grimmpp/audiobox-for-kids/case/OpenscadCase1.png

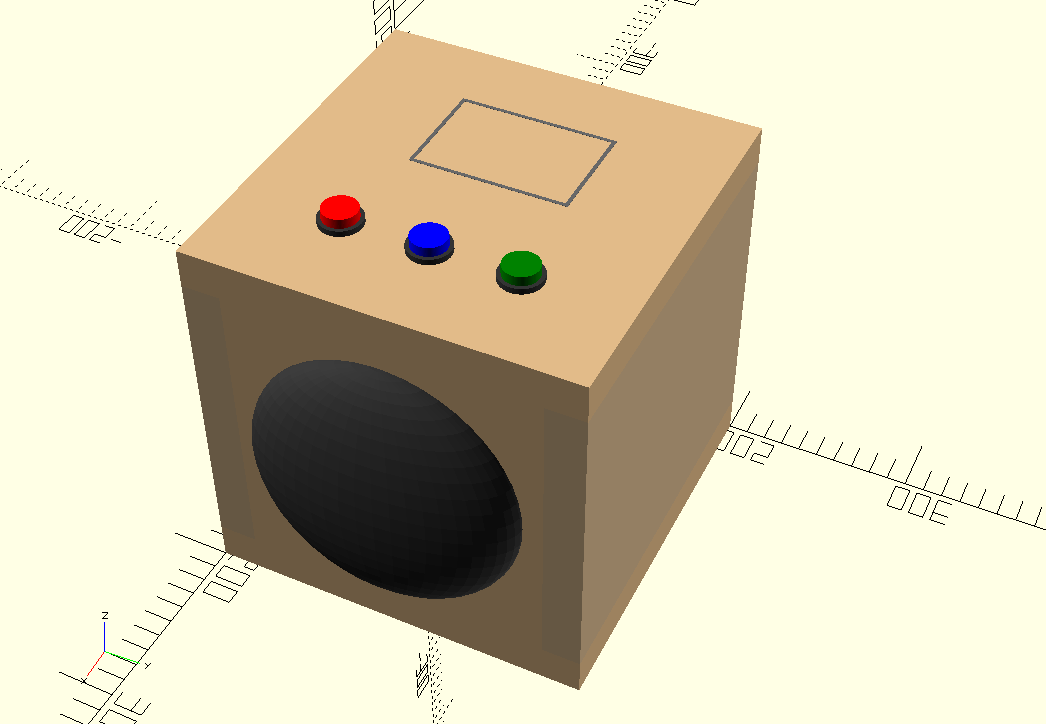
case/OpenscadCase1.png
