grimmpp/audiobox-for-kids/case/OpenscadCase2.png

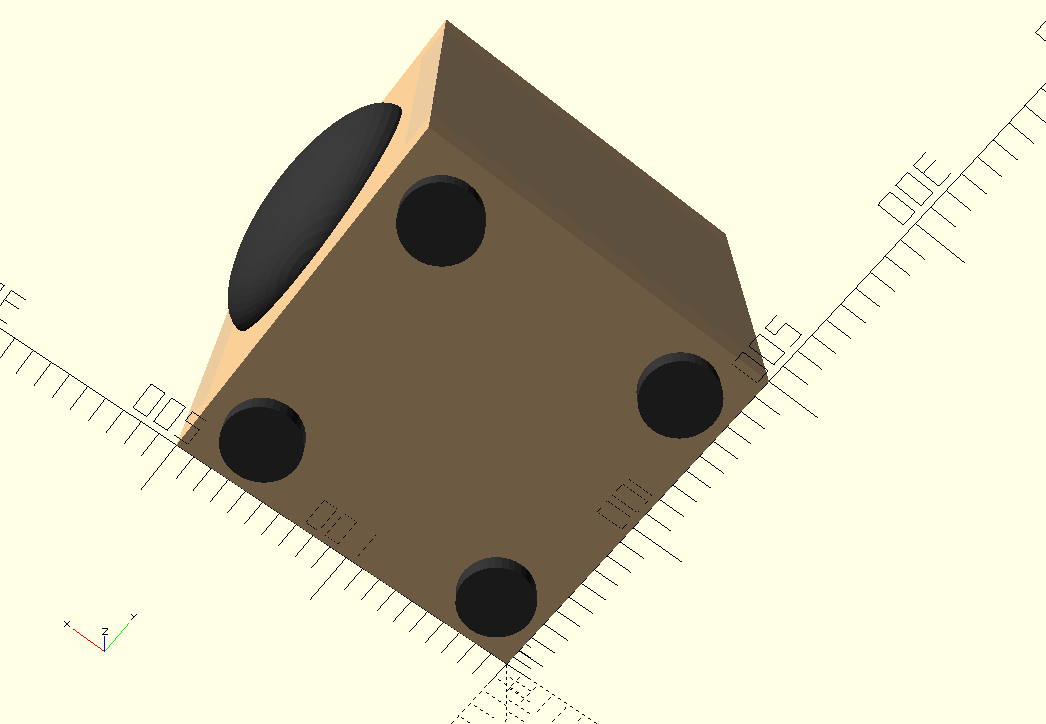
case/OpenscadCase2.png
