grimmpp/audiobox-for-kids/case/OpenscadCase3.png

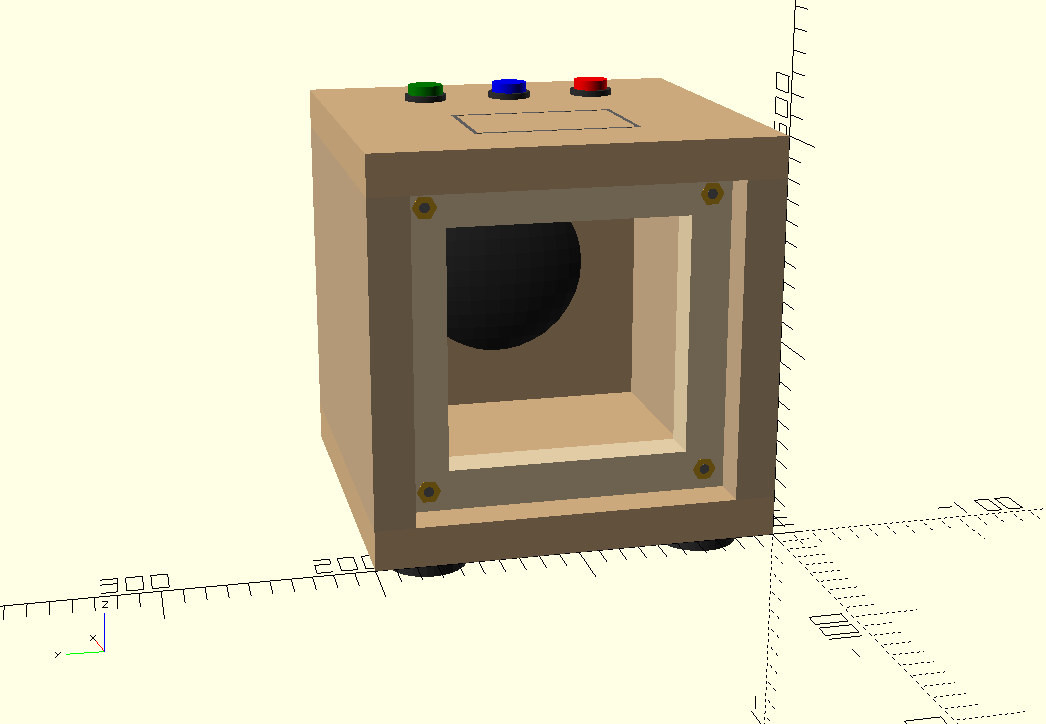
case/OpenscadCase3.png
