grimmpp/audiobox-for-kids/pics/20190909_121117.jpg

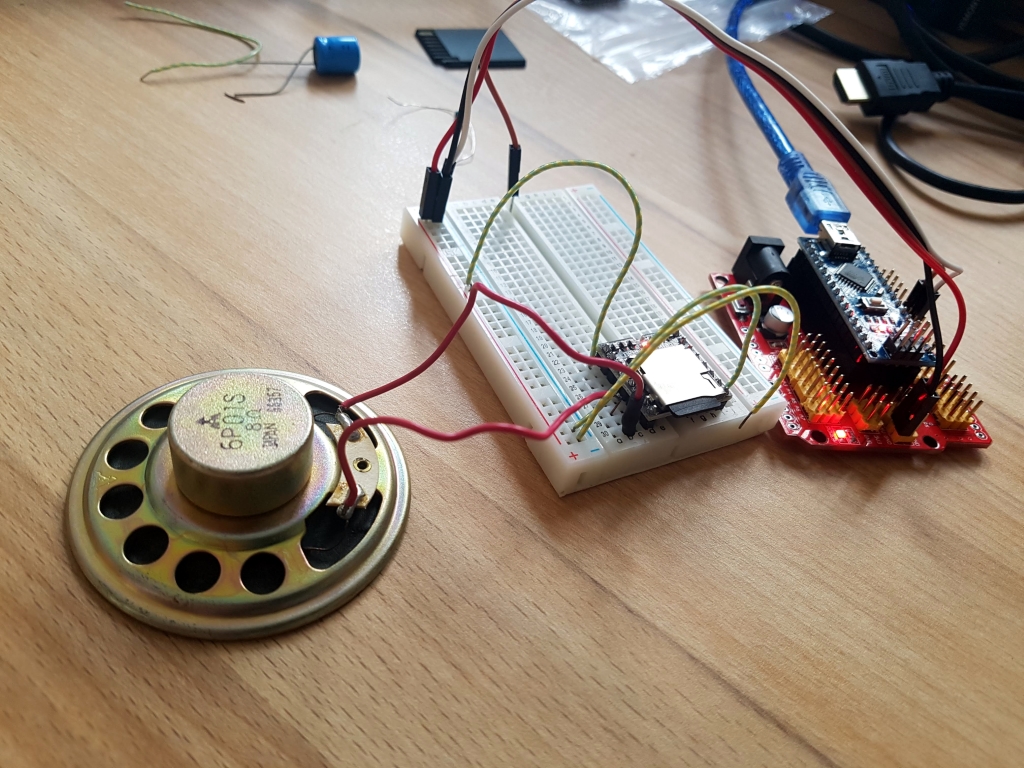
pics/20190909_121117.jpg
