grimmpp/audiobox-for-kids/pics/20190913_085506.jpg

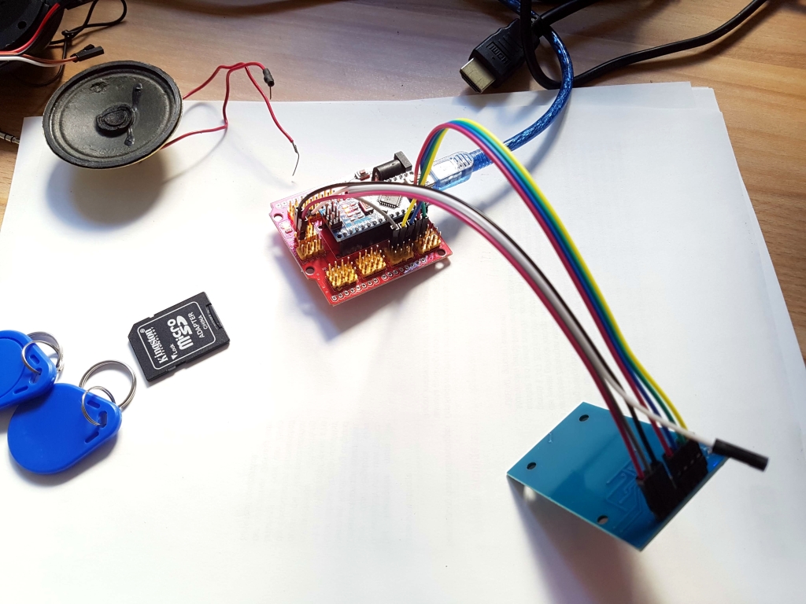
pics/20190913_085506.jpg
