grimmpp/audiobox-for-kids/pics/20190919_153926.jpg

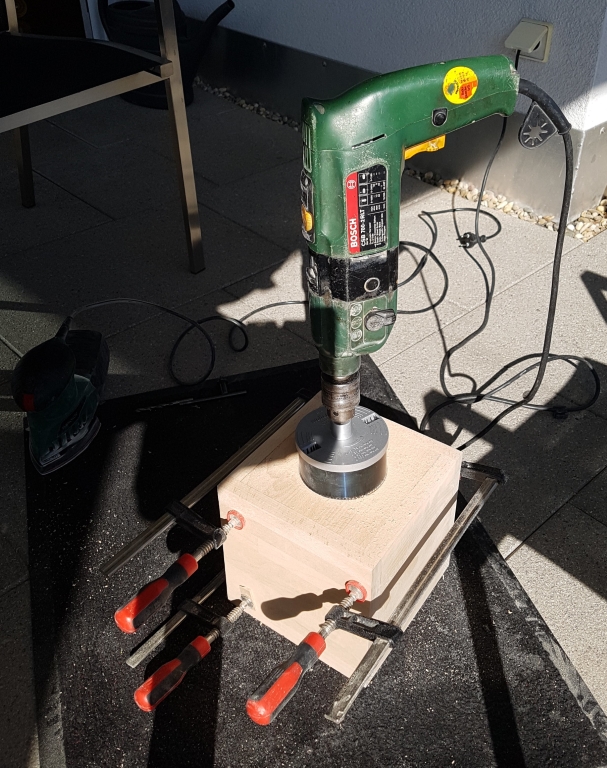
pics/20190919_153926.jpg
