grimmpp/audiobox-for-kids/pics/20190919_154714.jpg

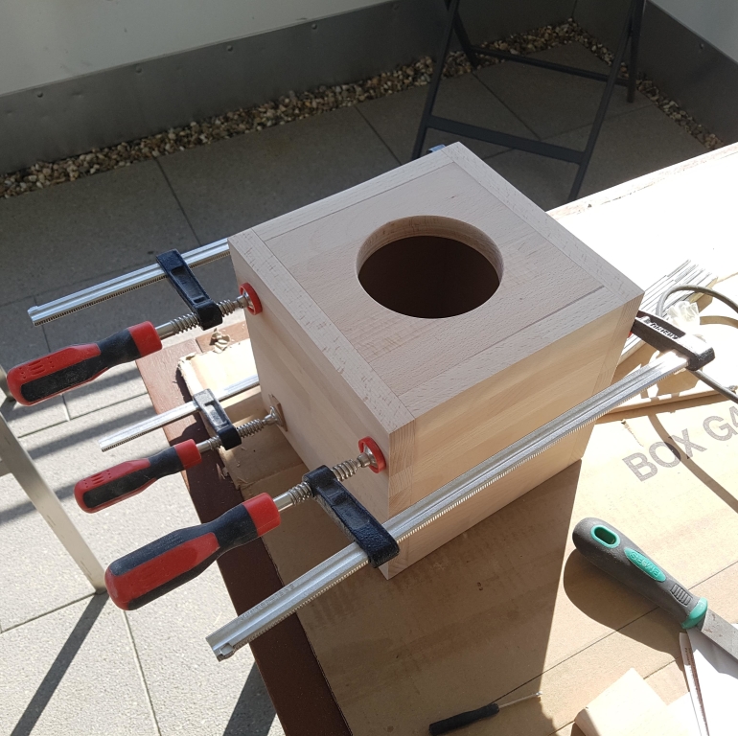
pics/20190919_154714.jpg
