grimmpp/audiobox-for-kids/pics/20190921_191524.jpg

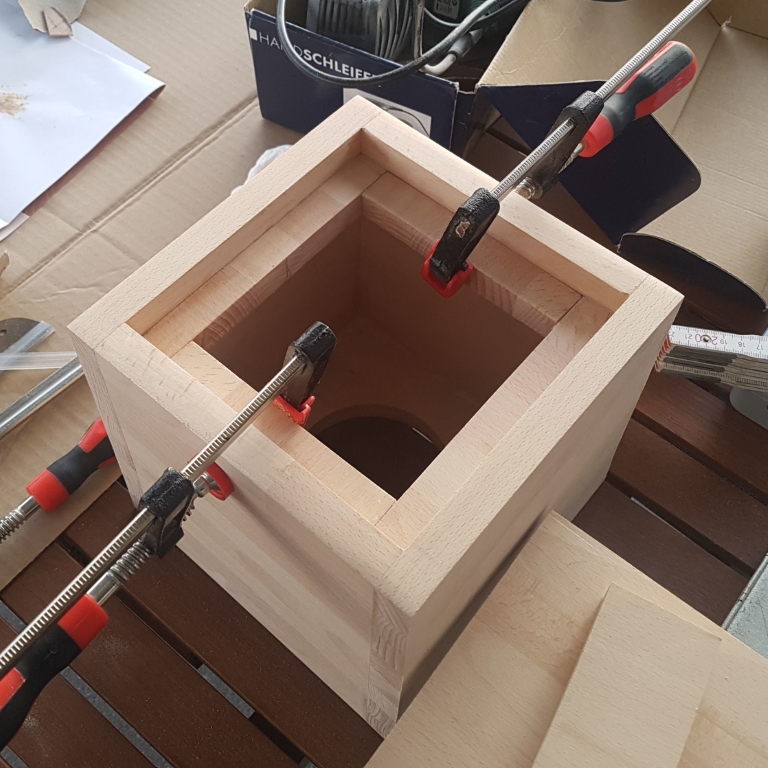
pics/20190921_191524.jpg
