grimmpp/audiobox-for-kids/pics/20190923_142010.jpg

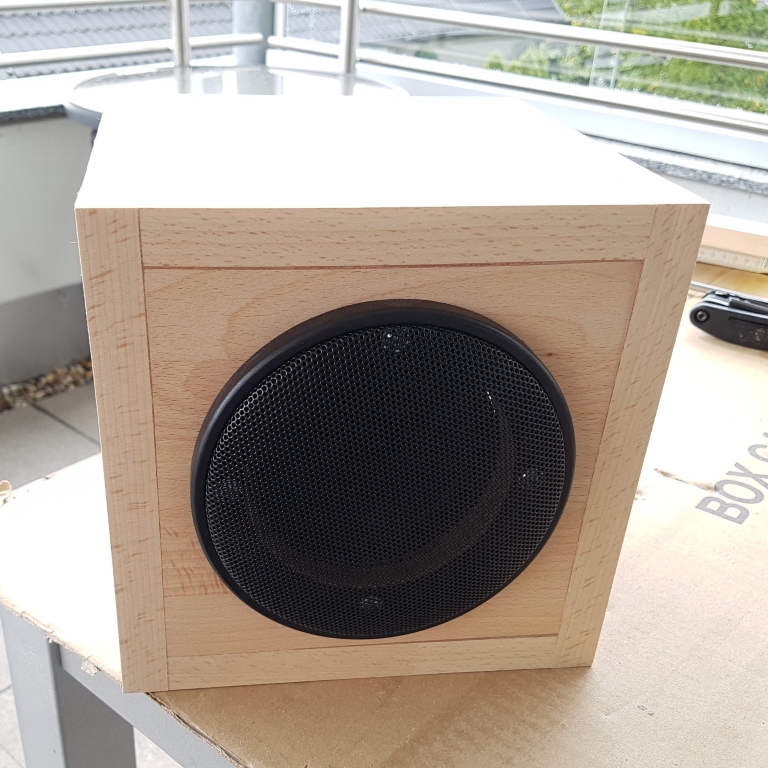
pics/20190923_142010.jpg
