grimmpp/audiobox-for-kids/pics/20190927_103004.jpg

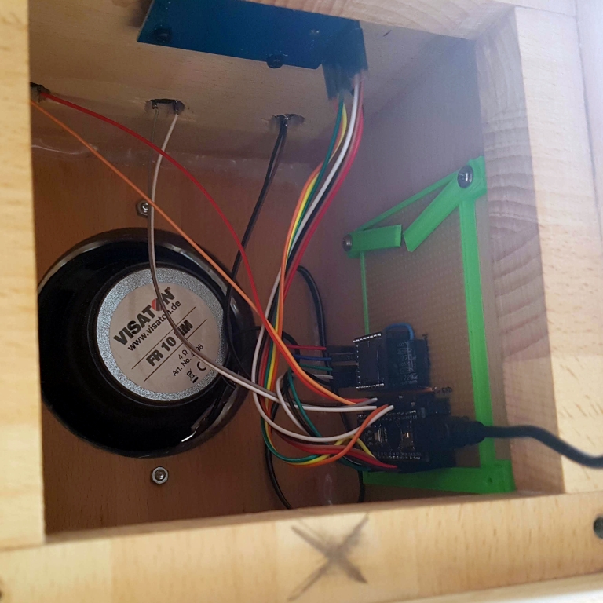
pics/20190927_103004.jpg
