grimmpp/audiobox-for-kids/pics/20190927_103024.jpg

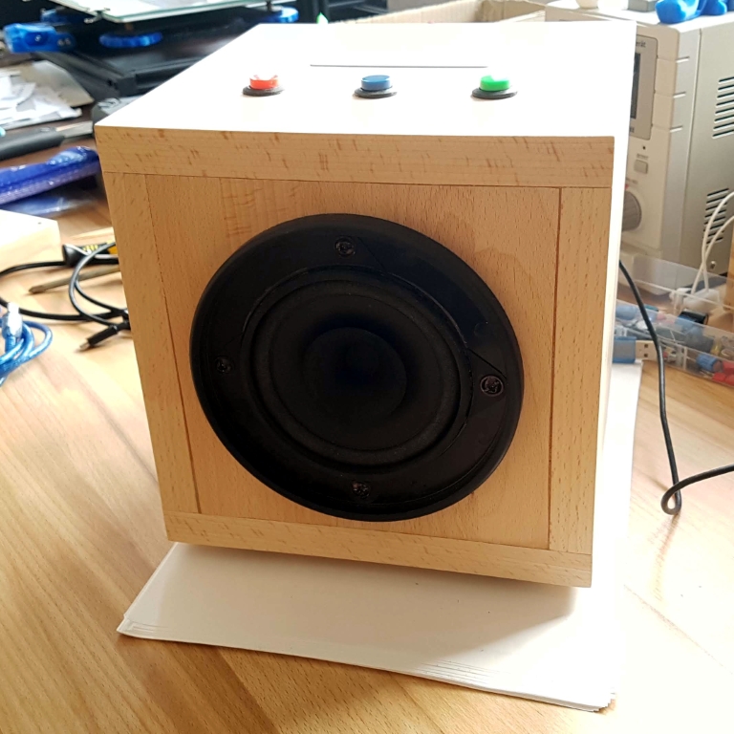
pics/20190927_103024.jpg
