grimmpp/audiobox-for-kids/pics/20190928_154832.jpg

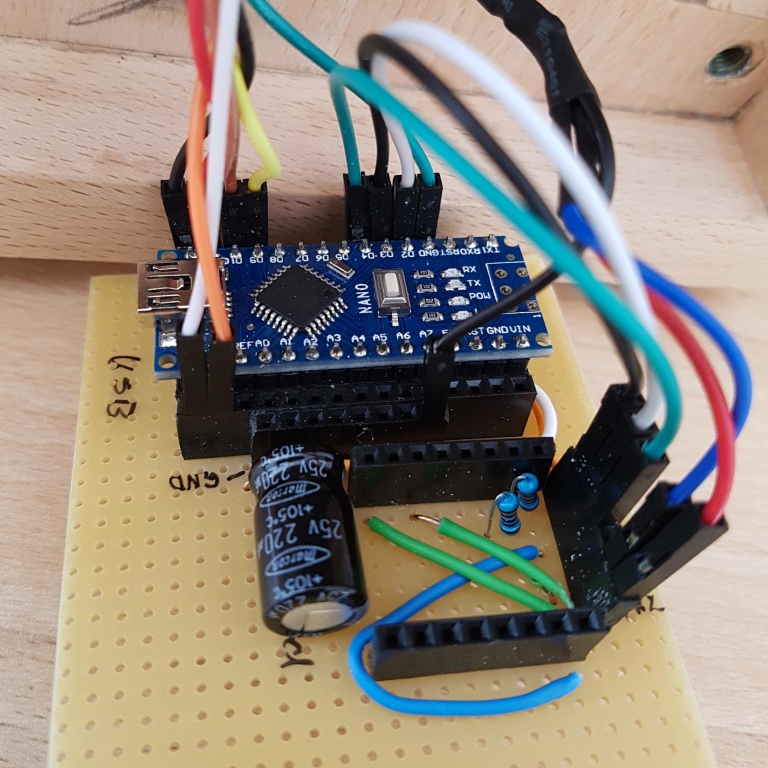
pics/20190928_154832.jpg
