grimmpp/audiobox-for-kids/pics/PHOTO_20191026_105717.jpg

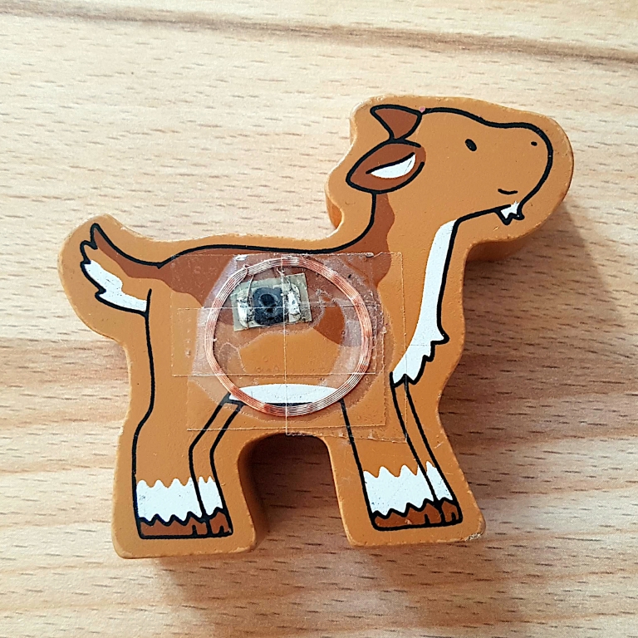
pics/PHOTO_20191026_105717.jpg
