grimmpp/audiobox-for-kids/pics/PHOTO_20191026_172718.jpg

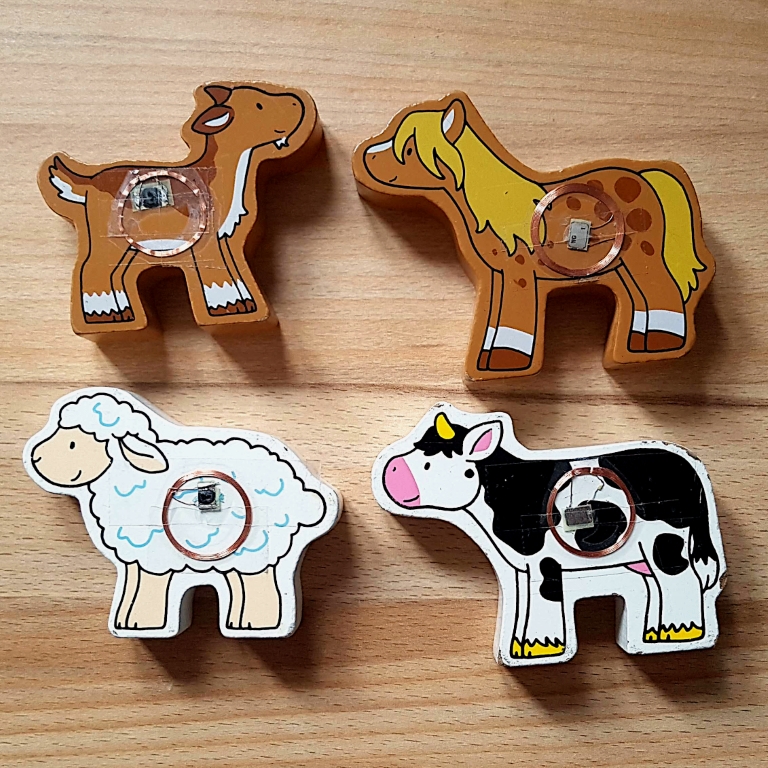
pics/PHOTO_20191026_172718.jpg
