grimmpp/audiobox-for-kids/pics/PHOTO_20191031_103545.jpg

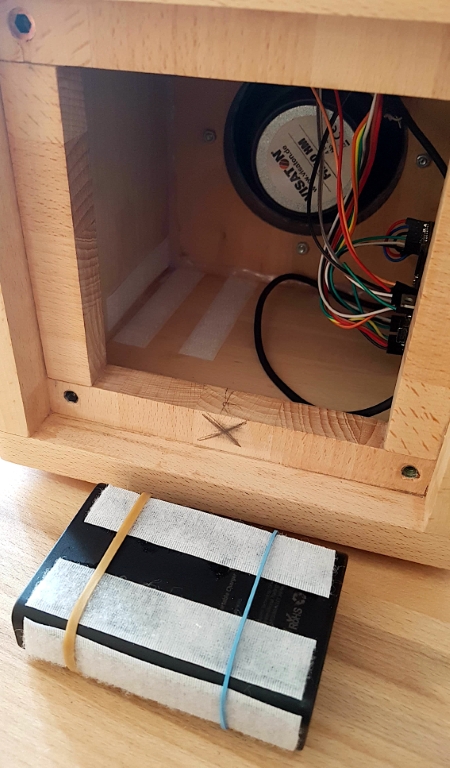
pics/PHOTO_20191031_103545.jpg
