grimmpp/audiobox-for-kids/pics/PHOTO_20191102_201601.jpg

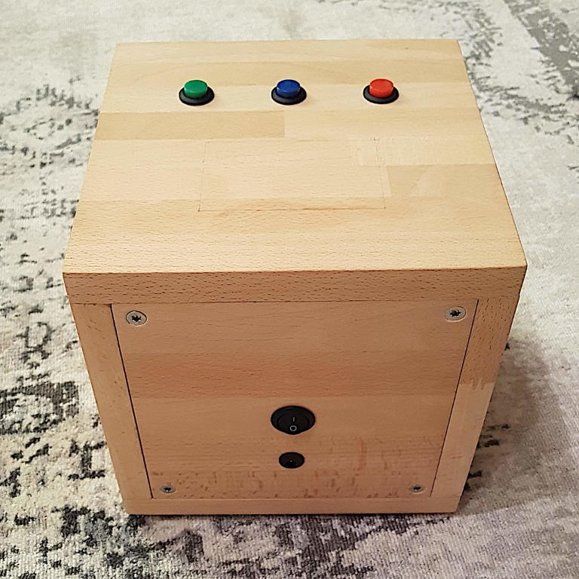
pics/PHOTO_20191102_201601.jpg
