grimmpp/audiobox-for-kids/pics/PHOTO_20191102_201644.jpg

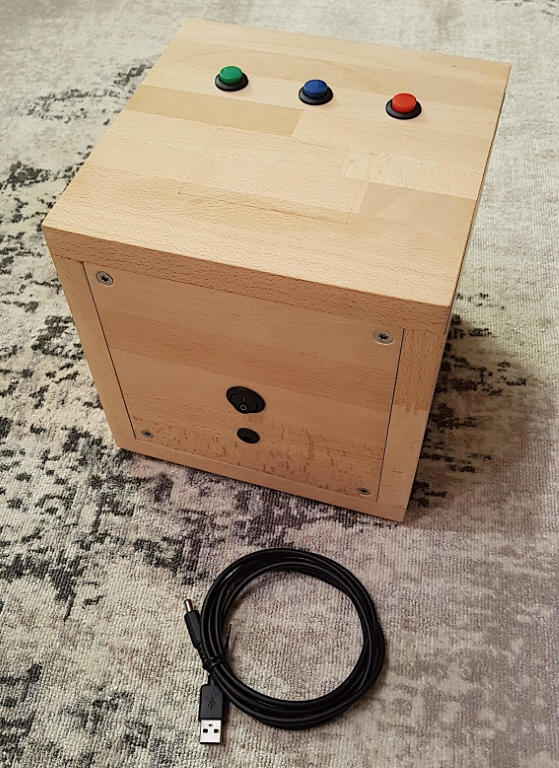
pics/PHOTO_20191102_201644.jpg
