grimmpp/audiobox-for-kids/pics/PHOTO_20191102_210108.jpg

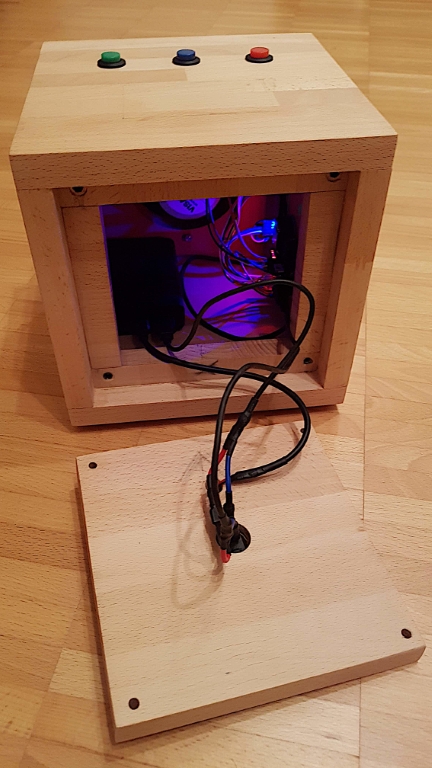
pics/PHOTO_20191102_210108.jpg
