grimmpp/audiobox-for-kids/print-template-rfid-card/FrameWhite.png

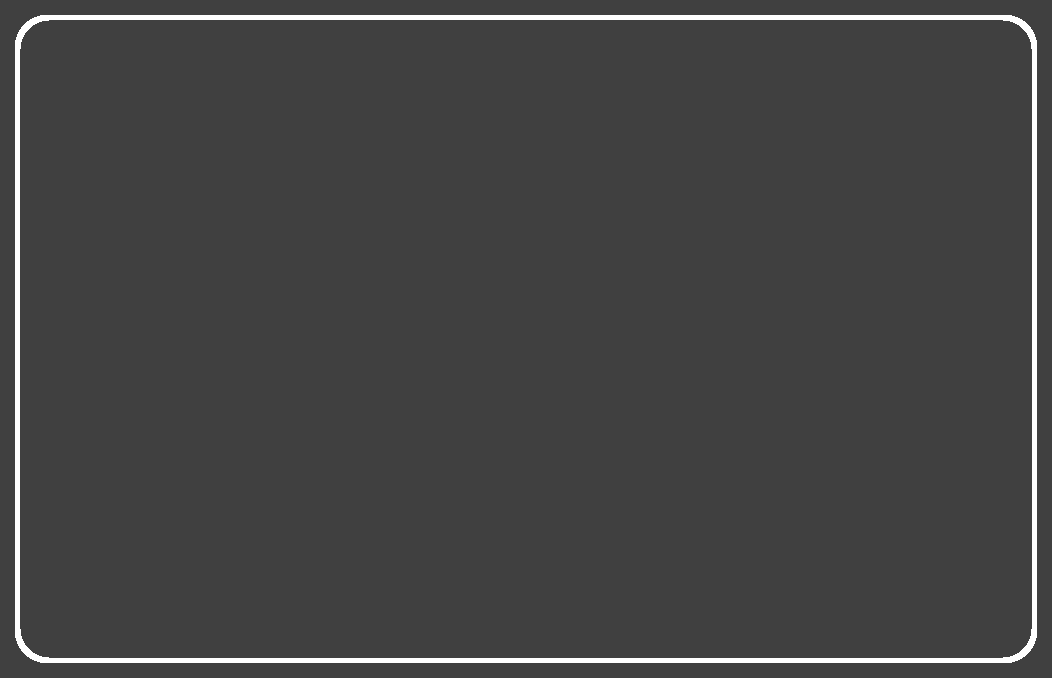
print-template-rfid-card/FrameWhite.png
