grimmpp/audiobox-for-kids/src/SystemSound.h

#ifndef Mp3CommandMap_H
#define Mp3CommandMap_H

#include <Arduino.h>


class SystemSound {
public:

    enum ID : uint16_t {
        UNKNOWN = 0,
        NEW_TAG = 300,
        TAG_LINKED = 310,
        MODE_RANDOM_EPISODE = 311,
        MODE_ALBUM = 312,
        MODE_PARTY = 313,
        MODE_SINGLE_TRACK = 314,
        MODE_AUDIO_BOOK = 315,
        ADMIN = 316,
        SELECT_FILE = 320,
        SAY_NUMBER_ASK = 330,
        SAY_NUMBER_NO = 331,
        SAY_NUMBER_YES = 332,
        BUTTON_SOUND = 350,
        TAG_OK = 400,
        ERROR = 401,
        START_SOUND = 500,
        RESET_TAG = 800,
        RESET_TAG_OK = 801,
        RESET_ABORTED = 802,
        RESET_OK = 999,
    };

    struct Mp3SystemSoundMap{
        ID systemSoundId;
        char const *name;
    };

    static Mp3SystemSoundMap MP3_SYSTEM_SOUND_MAP[21];

    static const char* GetSystemSoundById(uint16_t id) {

        for(uint16_t i = 0; i < sizeof(MP3_SYSTEM_SOUND_MAP) / sizeof(Mp3SystemSoundMap); i++) {
            if (id == MP3_SYSTEM_SOUND_MAP[i].systemSoundId) {
                return MP3_SYSTEM_SOUND_MAP[i].name;
            }
        }
        
        // Return unknown field.
        return MP3_SYSTEM_SOUND_MAP[0].name;
    }
};

#endif
